Nakul22/Sirius/aoa_performance/Output/aoa_error_cdf.png

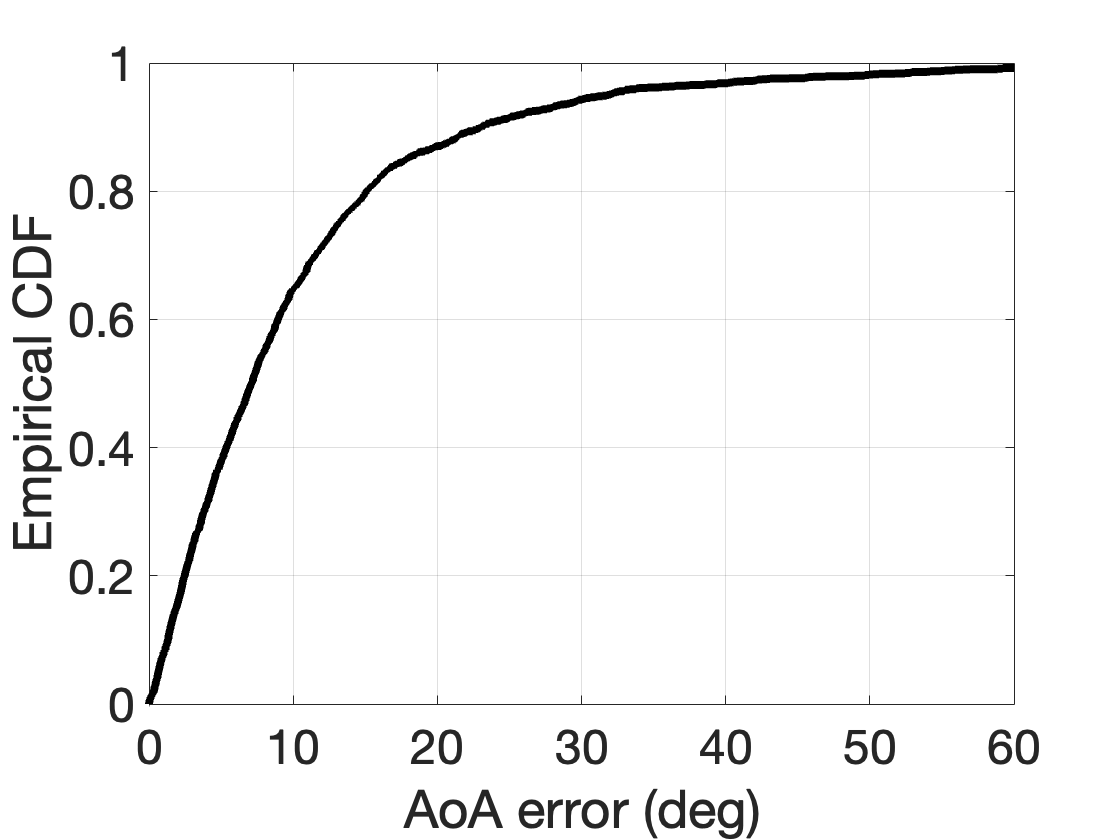
aoa_performance/Output/aoa_error_cdf.png
