Nakul22/Sirius/aoa_performance/Output/aoa_scatter_plot.png

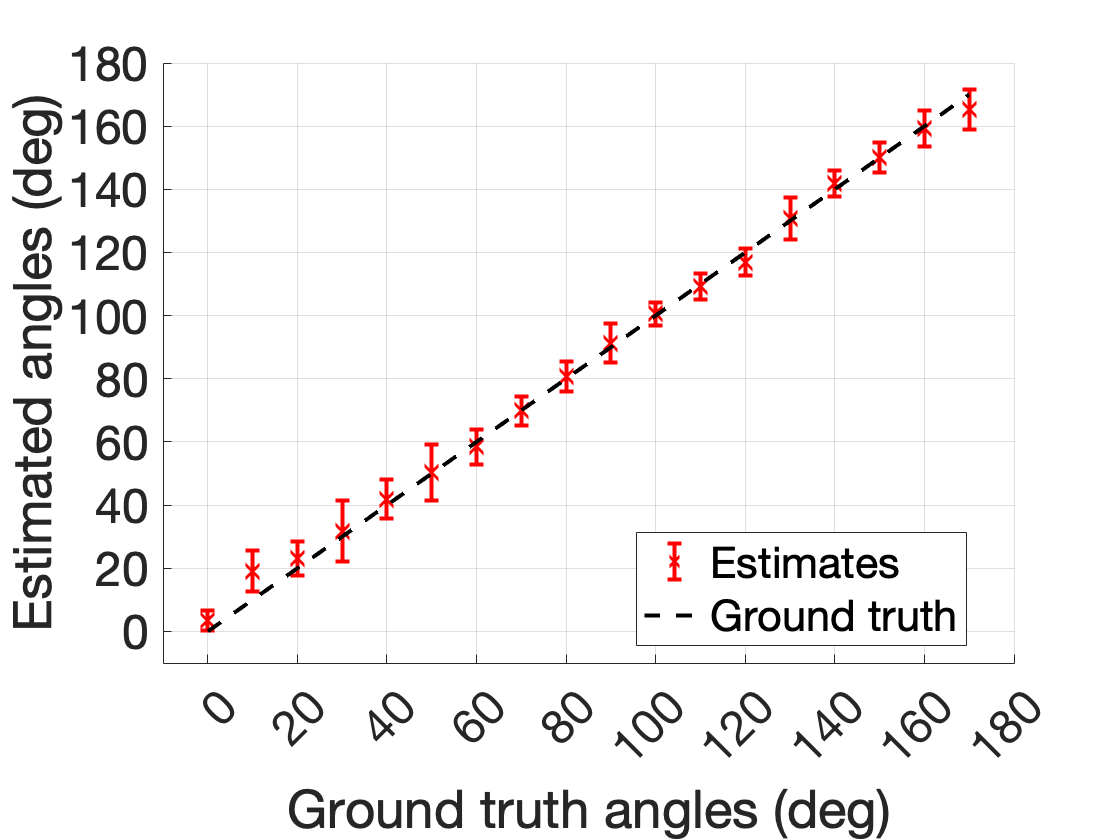
aoa_performance/Output/aoa_scatter_plot.png
