Nakul22/Sirius/localization_performance/Output/localization_error_cdf.png

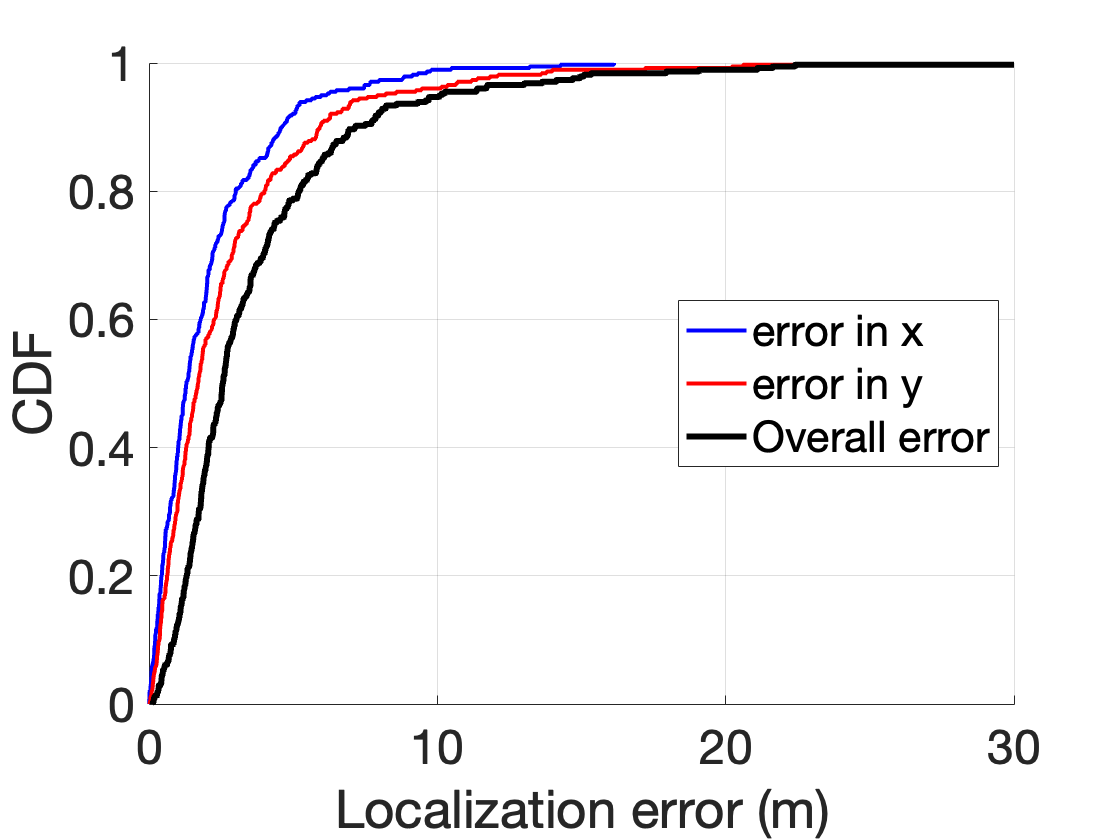
localization_performance/Output/localization_error_cdf.png
